fm4dd/pi-solar/cad/pi-solar E-3P main-bar v1.0.png

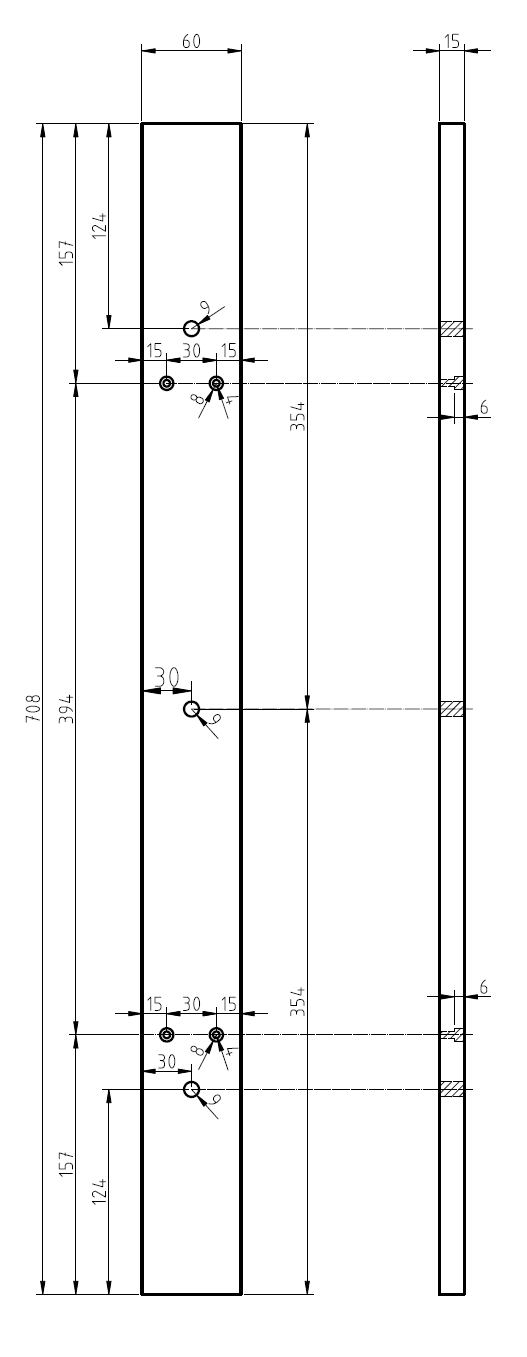
cad/pi-solar E-3P main-bar v1.0.png
