fm4dd/pi-solar/code/web/images/mppt-75-10.jpg

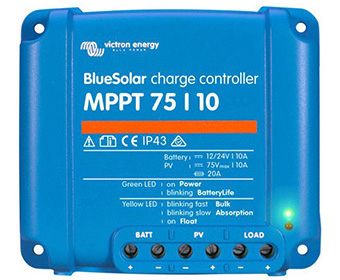
code/web/images/mppt-75-10.jpg
