fm4dd/pi-solar/code/web/images/solar-system-01.jpg

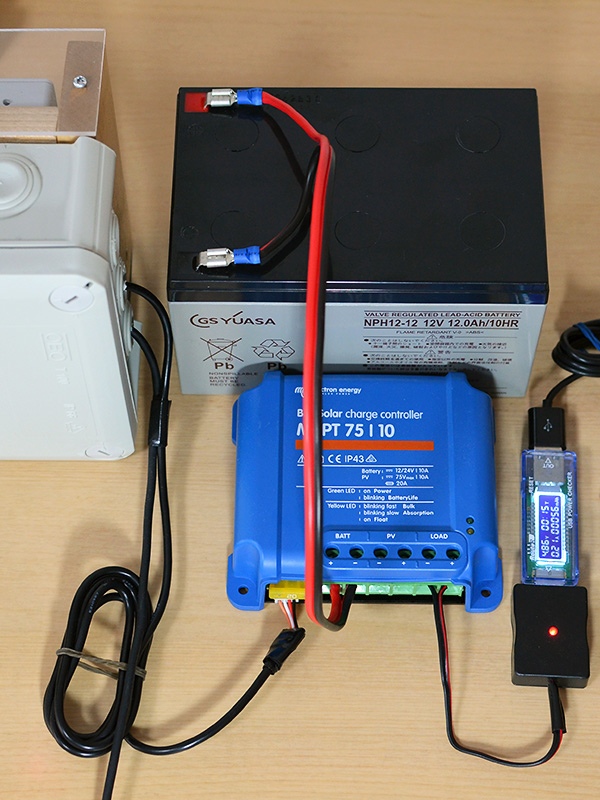
code/web/images/solar-system-01.jpg
