fm4dd/pi-solar/code/web/images/solar-system-02.jpg

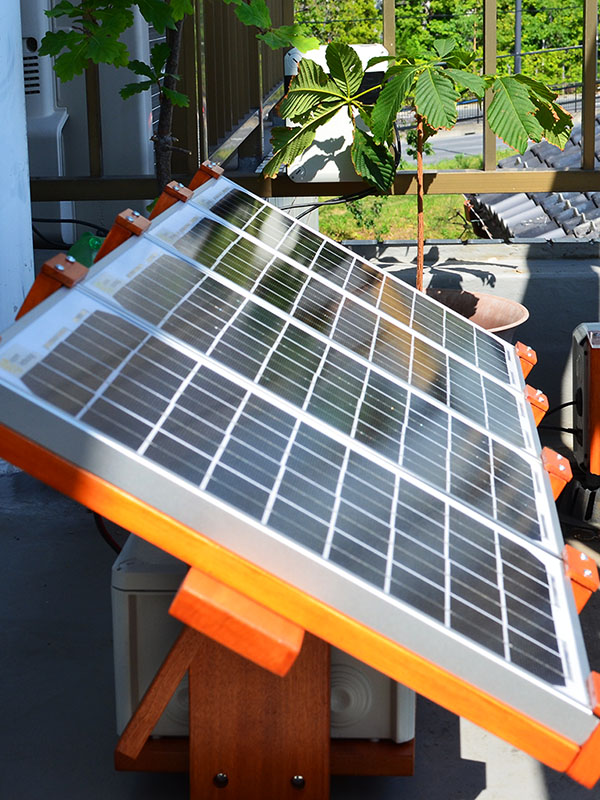
code/web/images/solar-system-02.jpg
