fm4dd/pi-solar/code/web/images/suntracker-01.jpg

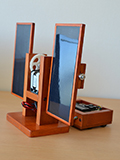
code/web/images/suntracker-01.jpg
