fm4dd/pi-solar/images/pi-solar serial connect2.jpg

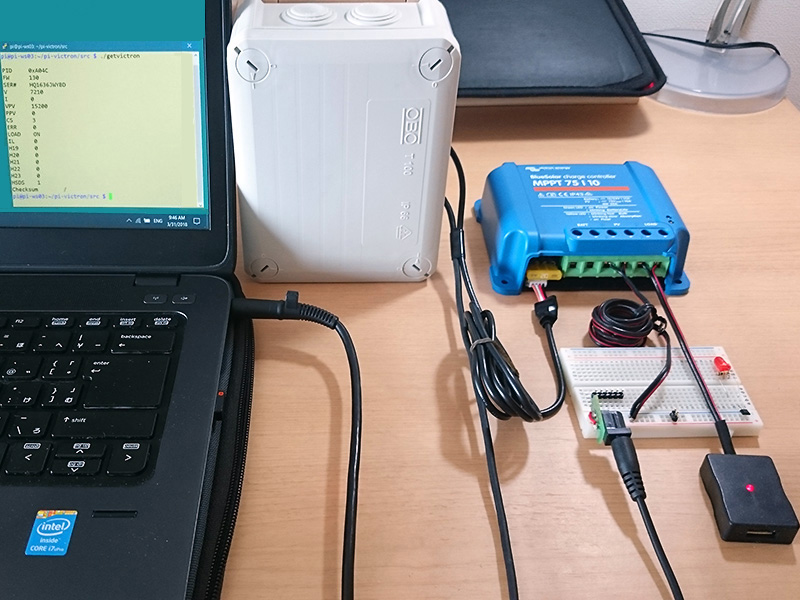
images/pi-solar serial connect2.jpg
